d29parkar/Autonomous_Weeding_Robot/CAD Models/connector.SLDPRT

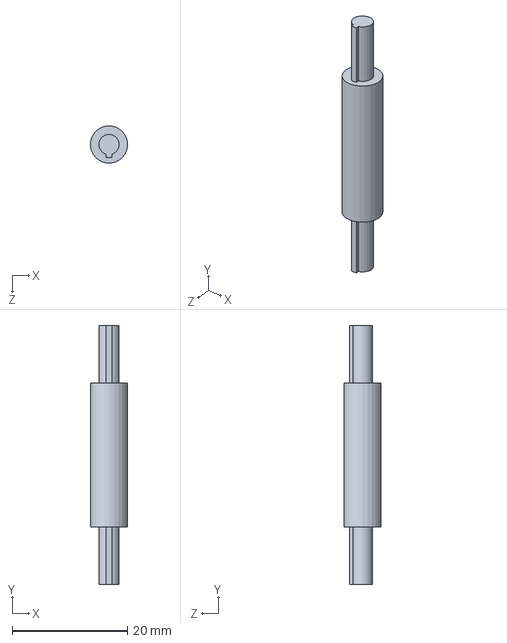
[picture p50: CAD file, 2022-12-19]
CAD Models/connector.SLDPRT
6.50 x 45.0 x 6.50 mm
