d29parkar/Autonomous_Weeding_Robot/CAD Models/motorV2.1.SLDPRT

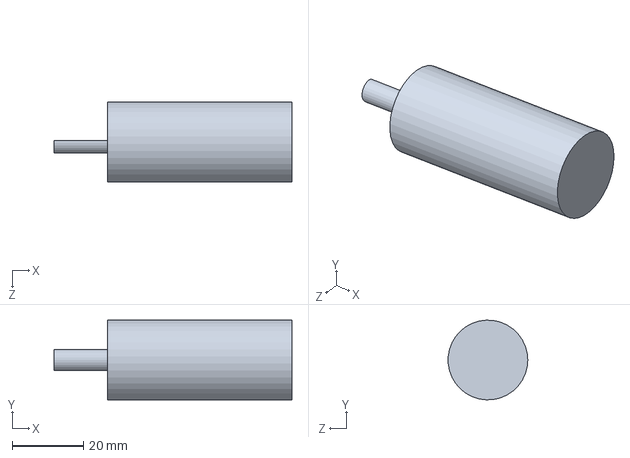
[picture p51: CAD file, 2022-12-19]
CAD Models/motorV2.1.SLDPRT
66.8 x 22.4 x 22.4 mm
