d29parkar/Autonomous_Weeding_Robot/CAD Models/Base_3Dprint_final.STL

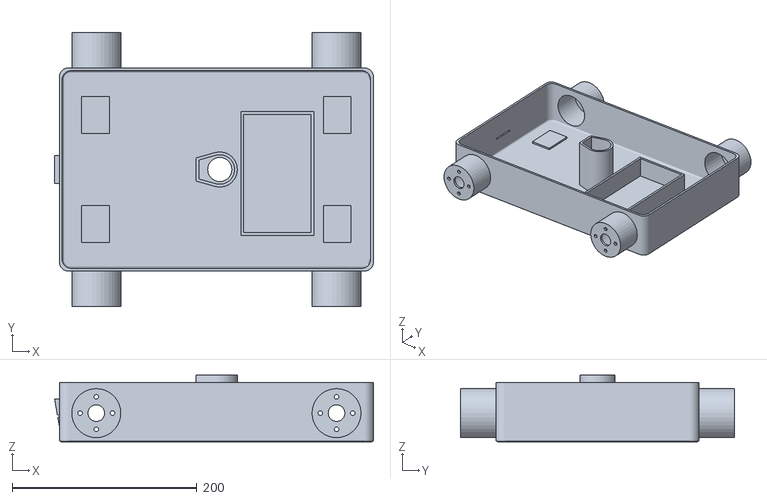
[picture p52: CAD file, 2022-12-19]
CAD Models/Base_3Dprint_final.STL
345.2 x 296.0 x 72.0
