d29parkar/Autonomous_Weeding_Robot/CAD Models/Base_3Dprint.STL

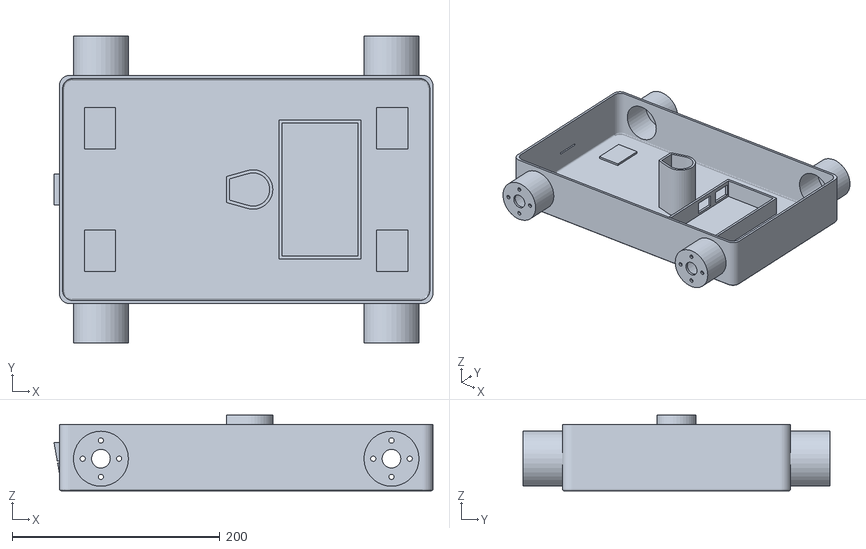
[picture p53: CAD file, 2022-12-19]
CAD Models/Base_3Dprint.STL
365.2 x 296.0 x 73.0
