d29parkar/Autonomous_Weeding_Robot/CAD Models/tool_casing.SLDPRT

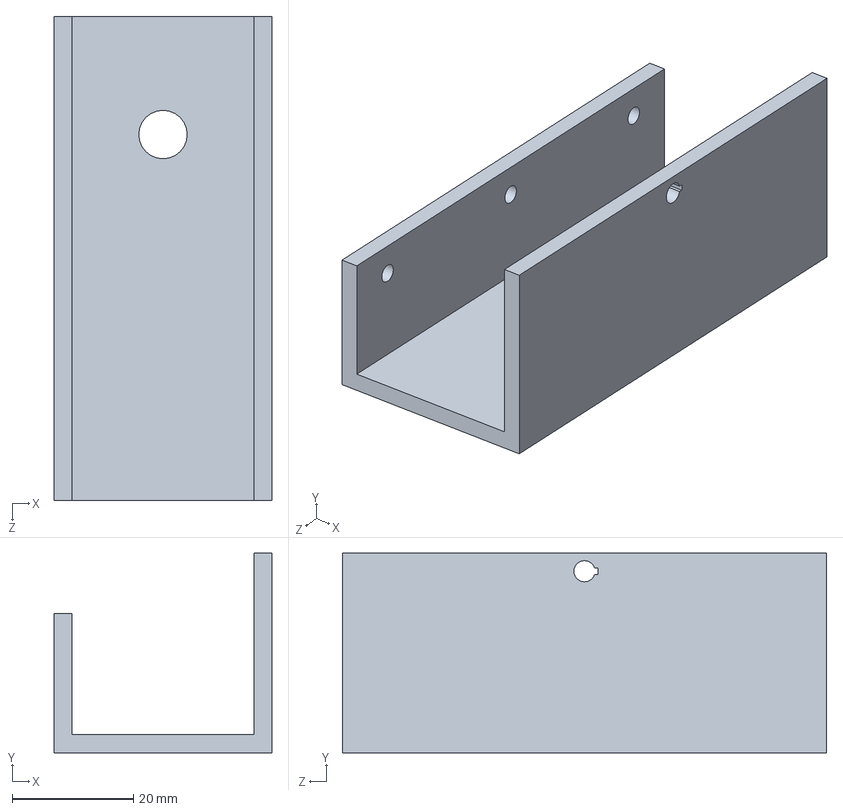
[picture p54: CAD file, 2022-12-19]
CAD Models/tool_casing.SLDPRT
36.0 x 33.0 x 80.0 mm
