d29parkar/Autonomous_Weeding_Robot/CAD Models/Part13.SLDPRT

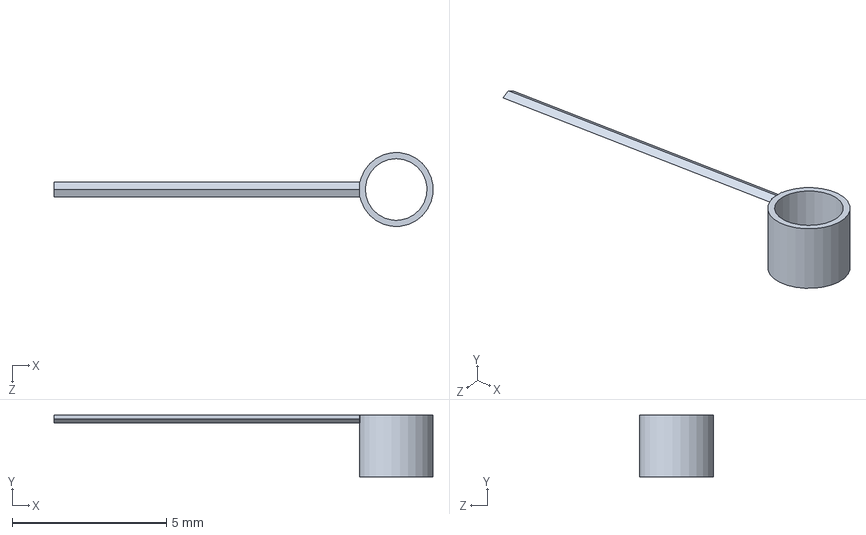
[picture p55: CAD file, 2022-12-19]
CAD Models/Part13.SLDPRT
12.3 x 2.00 x 2.39 mm
