d29parkar/Autonomous_Weeding_Robot/CAD Models/actuator_stroke.SLDPRT

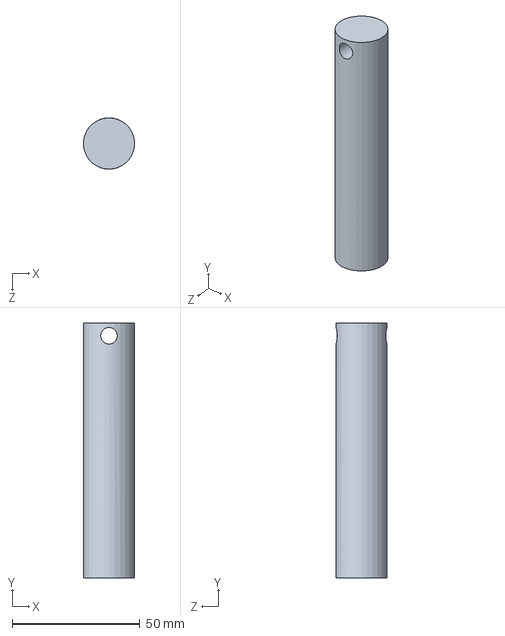
[picture p56: CAD file, 2022-12-19]
CAD Models/actuator_stroke.SLDPRT
20.1 x 100.0 x 20.1 mm
