d29parkar/Autonomous_Weeding_Robot/CAD Models/BO DC Motor.SLDPRT

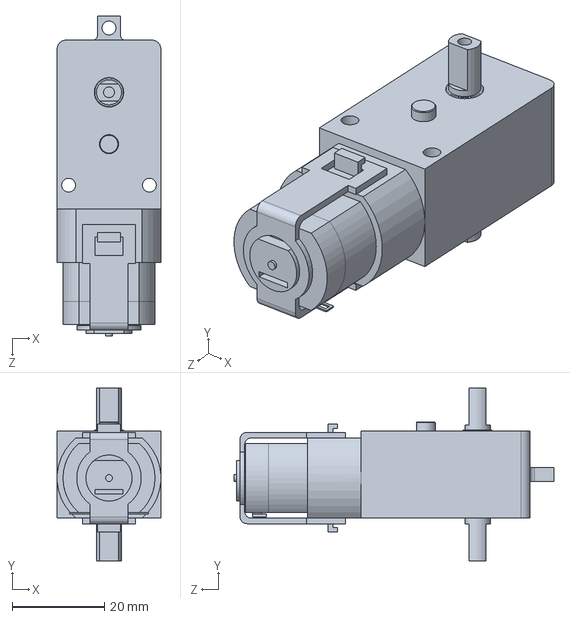
[picture p57: CAD file, 2022-12-19]
CAD Models/BO DC Motor.SLDPRT
22.5 x 37.4 x 69.3 mm
