d29parkar/Autonomous_Weeding_Robot/CAD Models/motor.SLDPRT

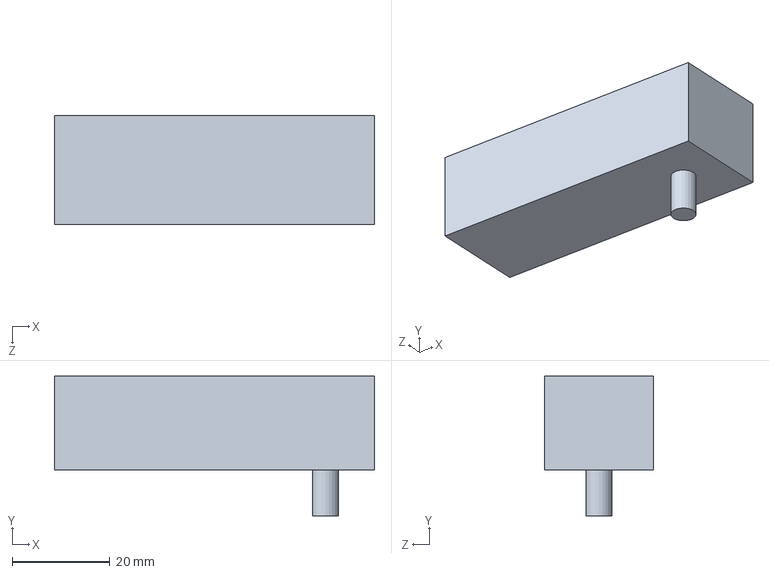
[picture p58: CAD file, 2022-12-19]
CAD Models/motor.SLDPRT
65.4 x 28.5 x 22.3 mm
