d29parkar/Autonomous_Weeding_Robot/CAD Models/Camera.SLDPRT

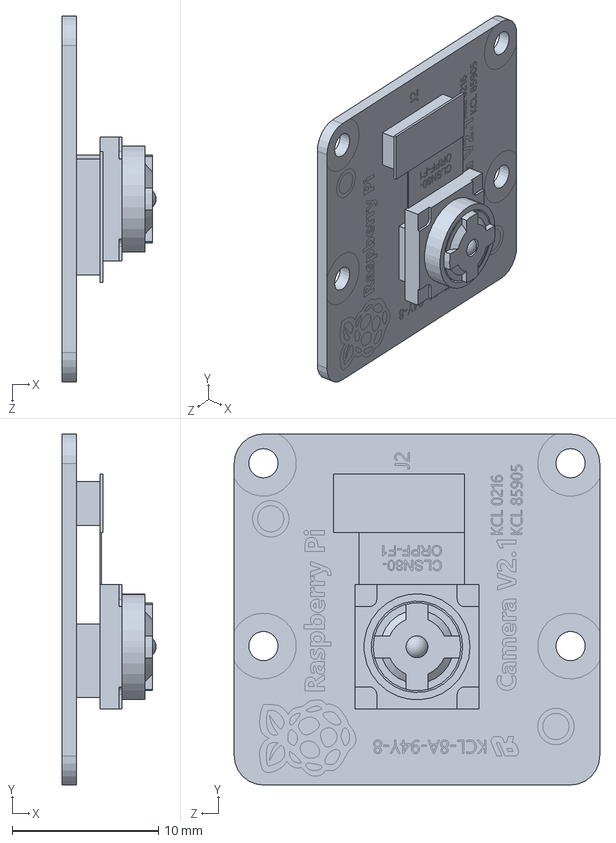
[picture p59: CAD file, 2022-12-19]
CAD Models/Camera.SLDPRT
6.45 x 24.0 x 25.0 mm
