d29parkar/Autonomous_Weeding_Robot/CAD Models/RelayBoardSLDPRT.SLDPRT

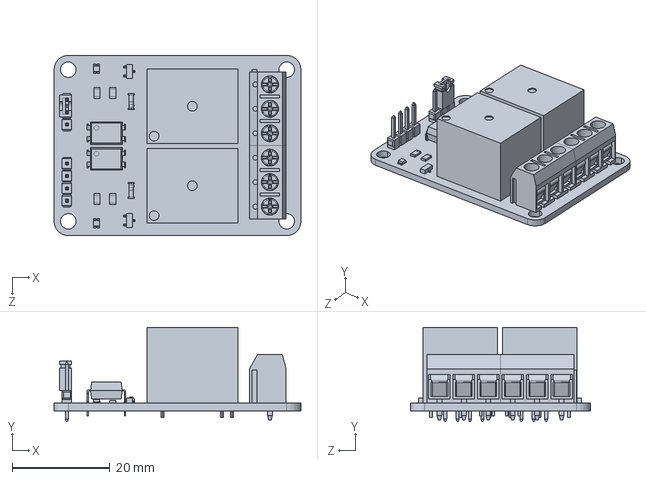
[picture p60: CAD file, 2022-12-19]
CAD Models/RelayBoardSLDPRT.SLDPRT
50.5 x 19.3 x 36.9 mm
